nigeljbs/MAE-342/figures/Dirtbike_Rider_No_Background.png

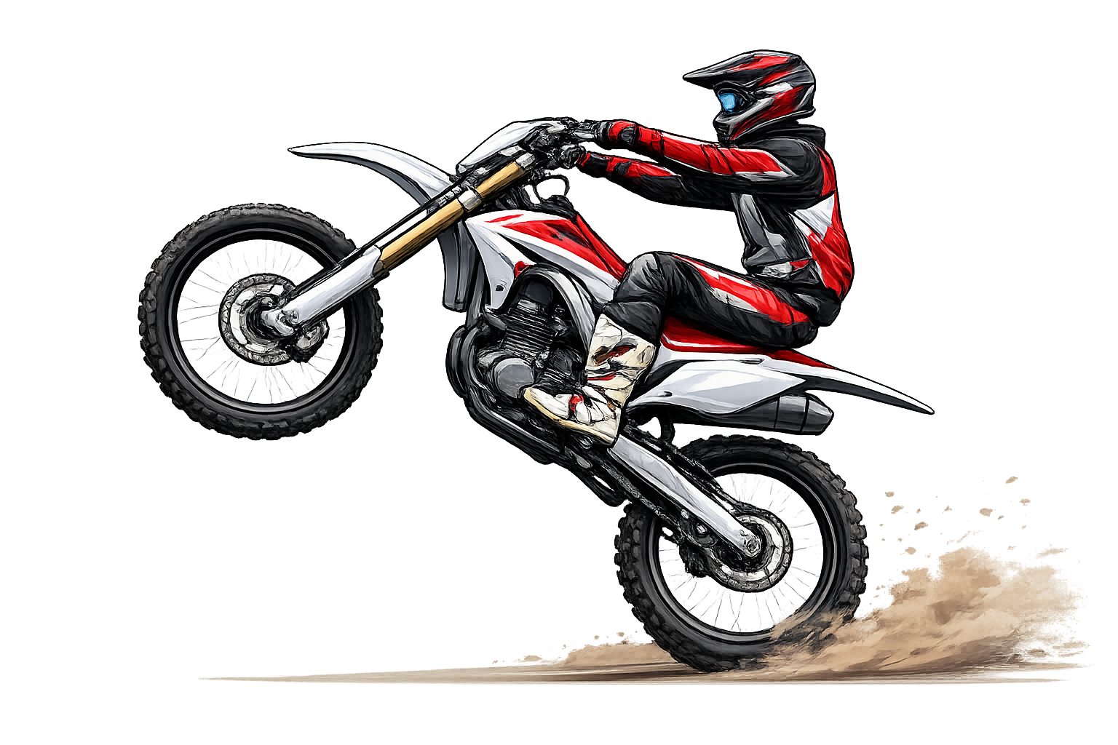
figures/Dirtbike_Rider_No_Background.png
