nigeljbs/MAE-342/figures/Exhaust_Spring_Dimensions.png

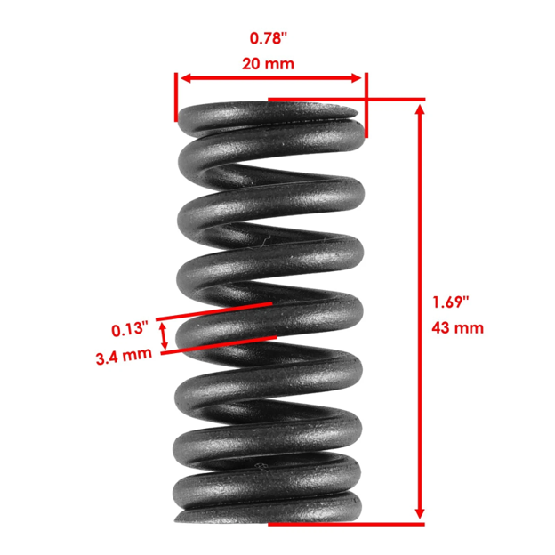
figures/Exhaust_Spring_Dimensions.png
