nigeljbs/MAE-342/figures/Exhaust_Valve_Dimensions.png

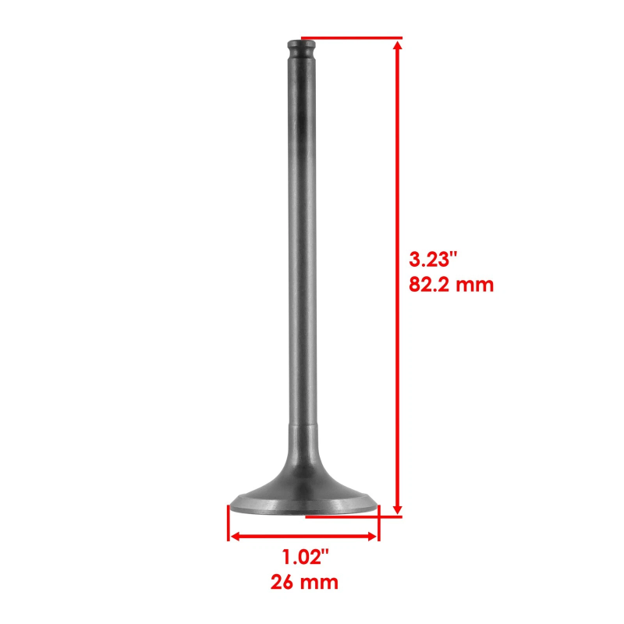
figures/Exhaust_Valve_Dimensions.png
