nigeljbs/MAE-342/figures/Motion.gif

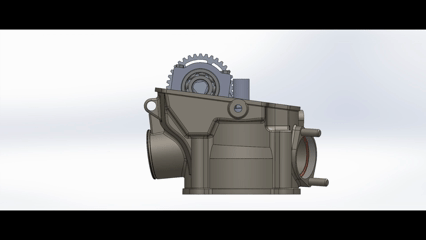
figures/Motion.gif
